kuenrg153/BitshokaNini_V1.1/3d/SOT-23-5_M5_MCH.step

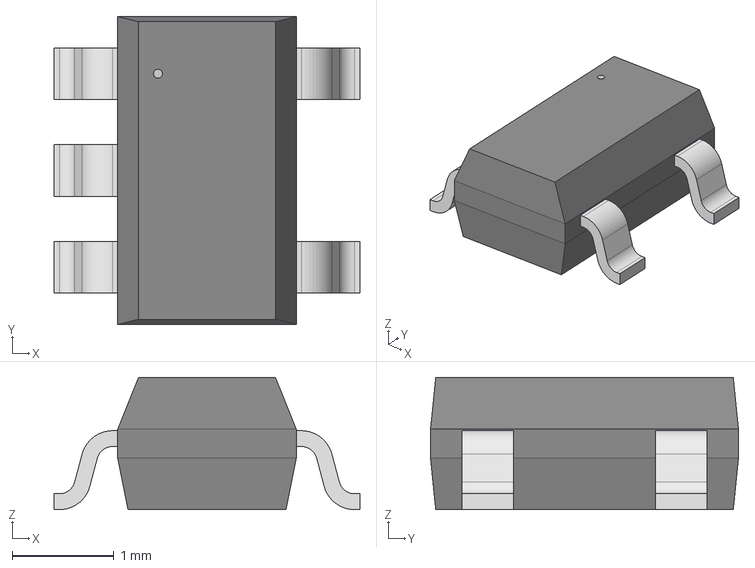
[picture p18: CAD file, 2025-06-05]
3d/SOT-23-5_M5_MCH.step
3.00 x 3.02 x 1.30 mm
