kuenrg153/BitshokaNini_V1.1/3d/DQH0008A.stp

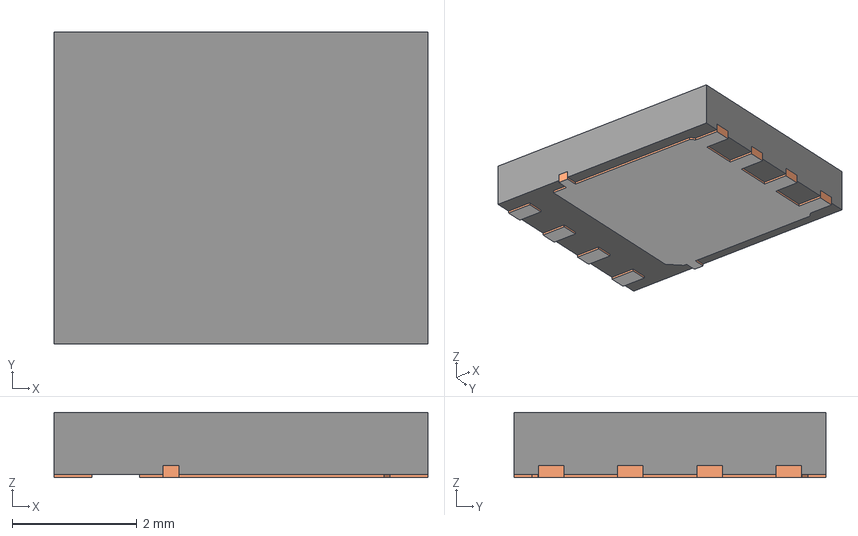
[picture p19: CAD file, 2025-06-05]
3d/DQH0008A.stp
6.00 x 5.00 x 1.05 mm
BODY-SON
FRAME-DQH0008A
PIN1-ID
