kuenrg153/BitshokaNini_V1.1/3d/Bitaxe_Heatsink.step

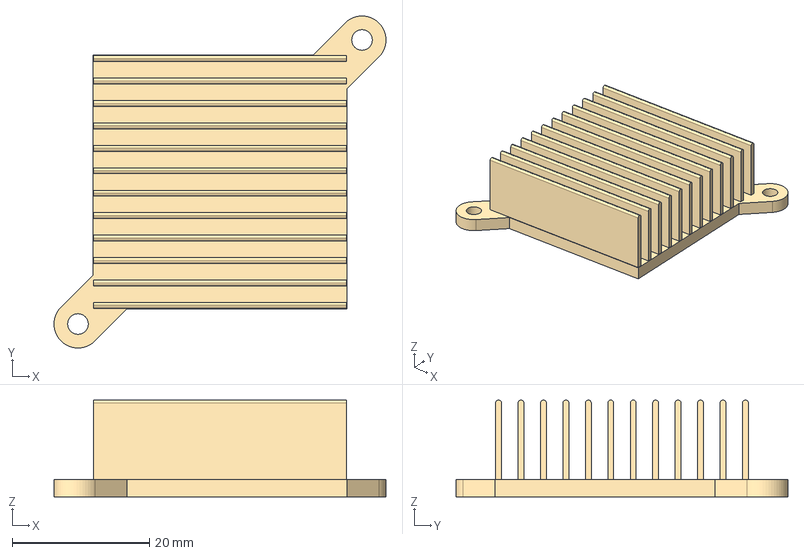
[picture p20: CAD file, 2025-06-05]
3d/Bitaxe_Heatsink.step
48.4 x 48.4 x 14.1 mm
