kuenrg153/BitshokaNini_V1.1/3d/oscillator3.2x2.5.step

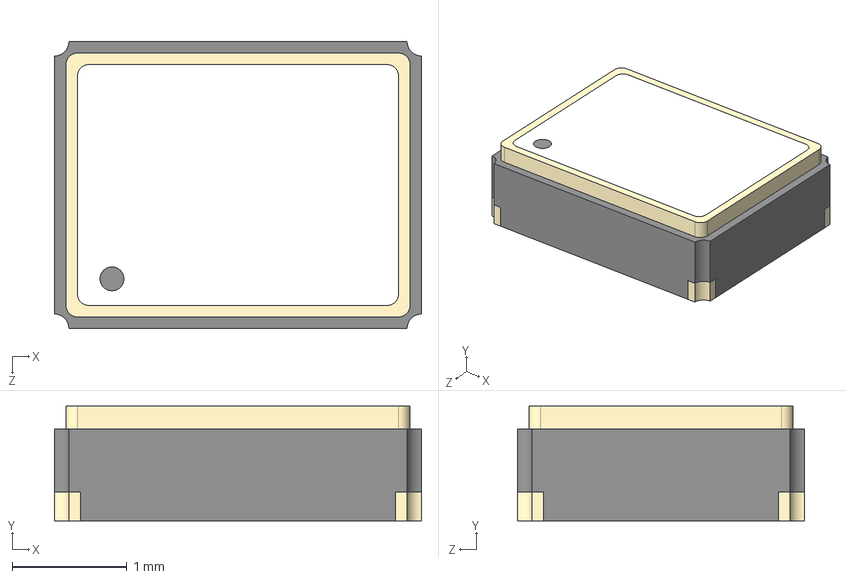
[picture p21: CAD file, 2025-06-05]
3d/oscillator3.2x2.5.step
3.20 x 1.00 x 2.50 mm
