kuenrg153/BitshokaNini_V1.1/3d/c-63862-1-r-3d.stp

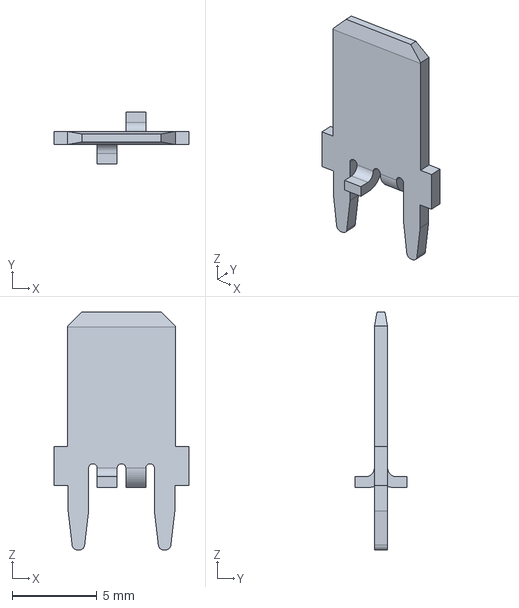
[picture p22: CAD file, 2025-06-05]
3d/c-63862-1-r-3d.stp
7.92 x 3.07 x 14.0 mm
