kuenrg153/BitshokaNini_V1.1/3d/2R5TPE220MAFB.step

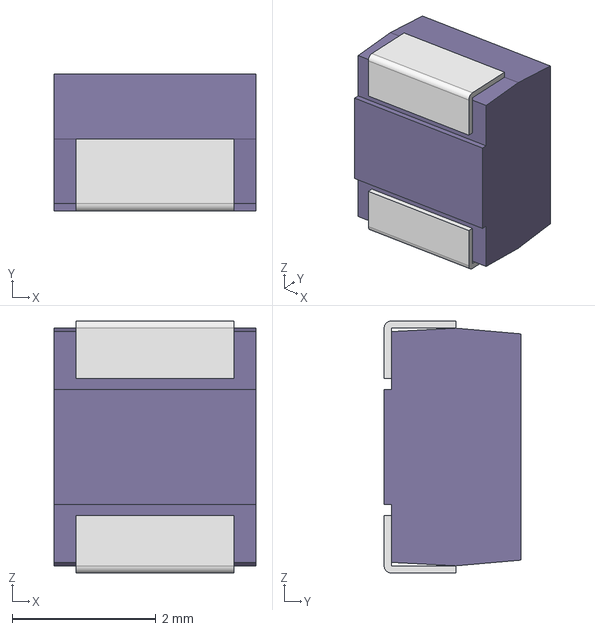
[picture p23: CAD file, 2025-06-05]
3d/2R5TPE220MAFB.step
2.80 x 1.90 x 3.50 mm
mold-B2
flame-B2 x 2
