kuenrg153/BitshokaNini_V1.1/3d/CS1213AG-tr.stp

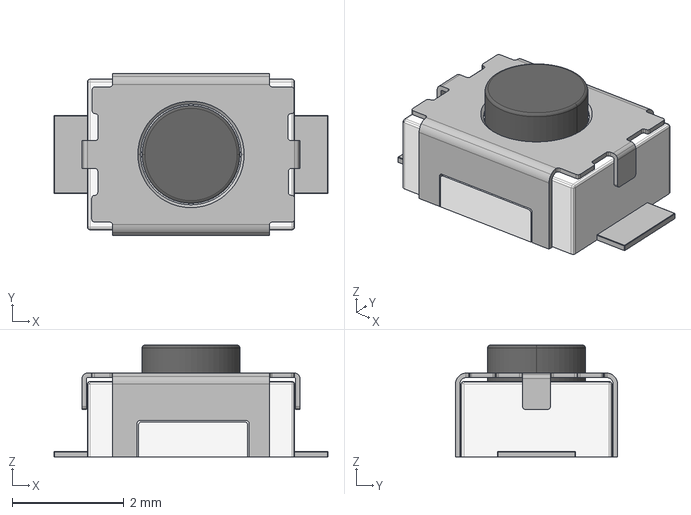
[picture p24: CAD file, 2025-06-05]
3d/CS1213AG-tr.stp
4.90 x 2.90 x 2.00 mm
