kuenrg153/BitshokaNini_V1.1/3d/CX3225SB16000H0FLJCC.STEP

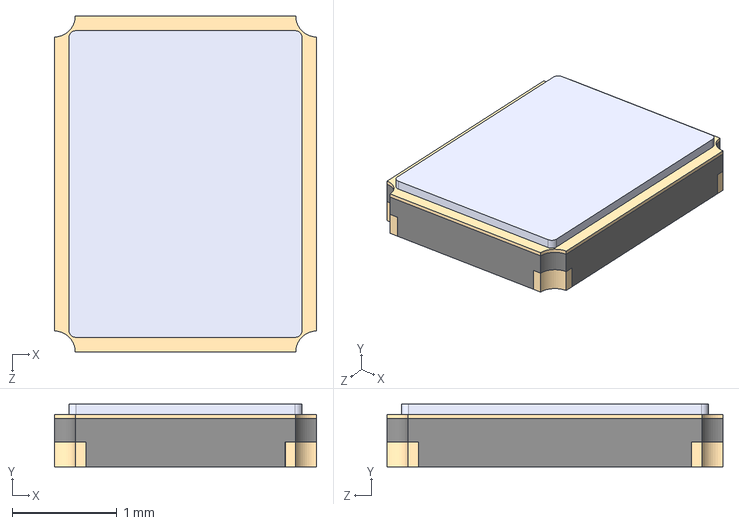
[picture p26: CAD file, 2025-06-05]
3d/CX3225SB16000H0FLJCC.STEP
2.50 x 0.6 x 3.20 mm
