kuenrg153/BitshokaNini_V1.1/3d/SN74AXC1T45DBVR.STEP

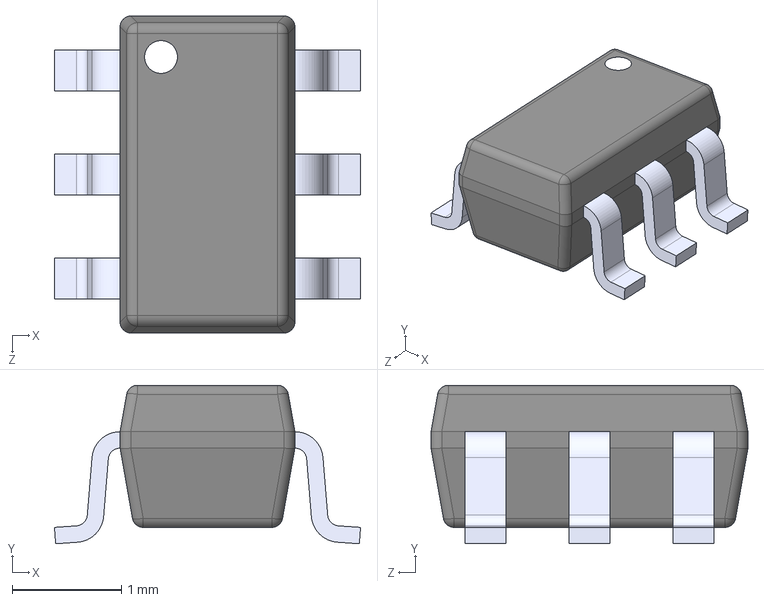
[picture p27: CAD file, 2025-06-05]
3d/SN74AXC1T45DBVR.STEP
2.80 x 1.45 x 2.90 mm
