kuenrg153/BitshokaNini_V1.1/3d/21-0164B_L622-1_MXM.step

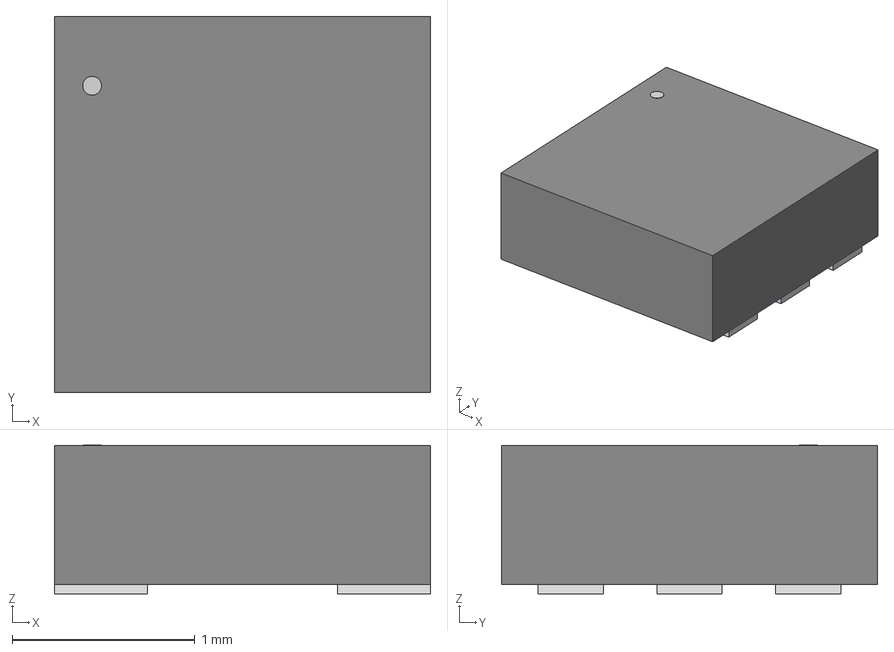
[picture p30: CAD file, 2025-06-05]
3d/21-0164B_L622-1_MXM.step
2.06 x 2.06 x 0.815 mm
