kuenrg153/BitshokaNini_V1.1/3d/54-00164.STEP

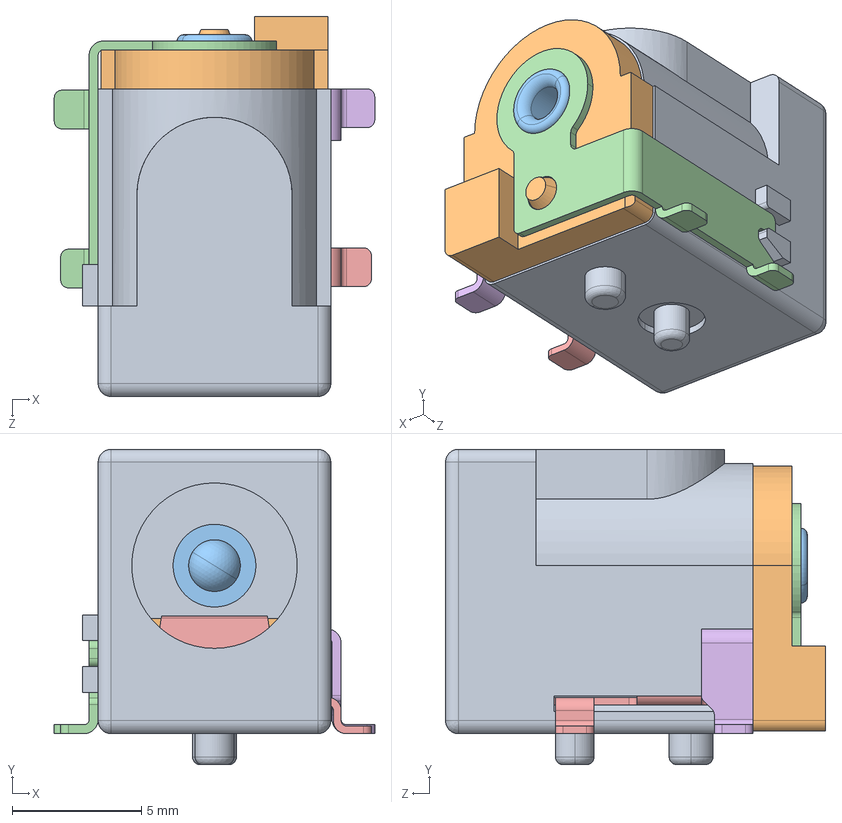
[picture p31: CAD file, 2025-06-05]
3d/54-00164.STEP
12.4 x 12.2 x 14.7 mm
54-00164_shell
54-00164_insulator
54-00164_center
54-00164_center contact
54-00164_spring contact
54-00164_shell contact
