kuenrg153/BitshokaNini_V1.1/3d/CUI_DEVICES_PJ-002AH.step

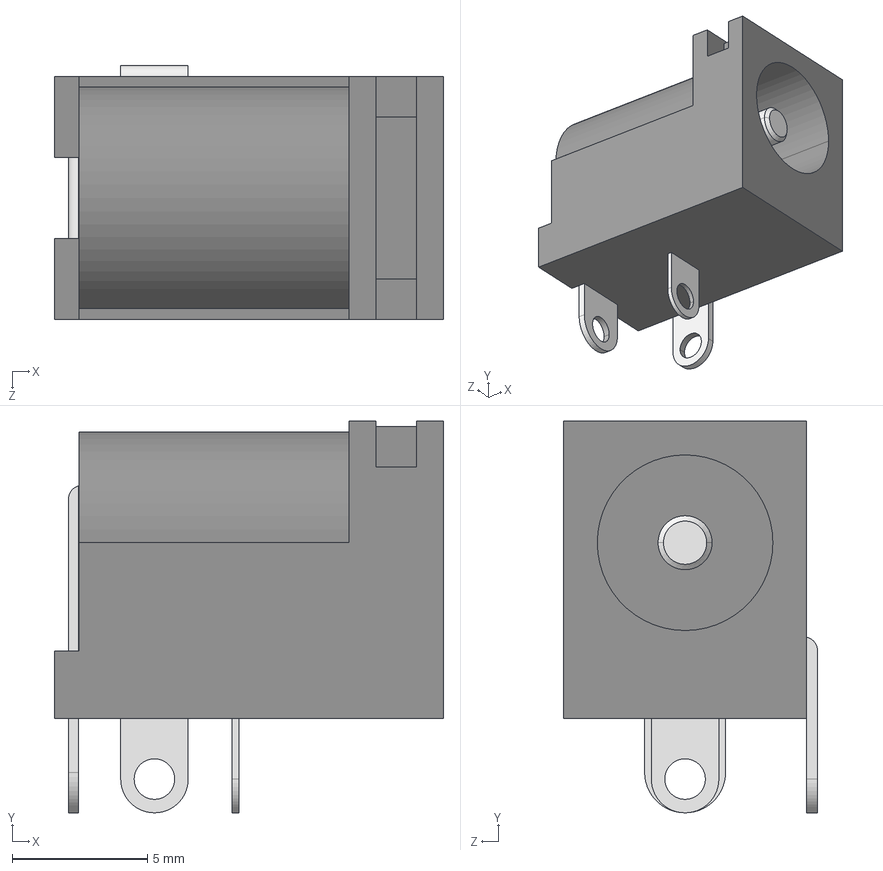
[picture p32: CAD file, 2025-06-05]
3d/CUI_DEVICES_PJ-002AH.step
14.4 x 14.5 x 9.40 mm
