kuenrg153/BitshokaNini_V1.1/3d/CUI_DEVICES_PJ-037AH.step

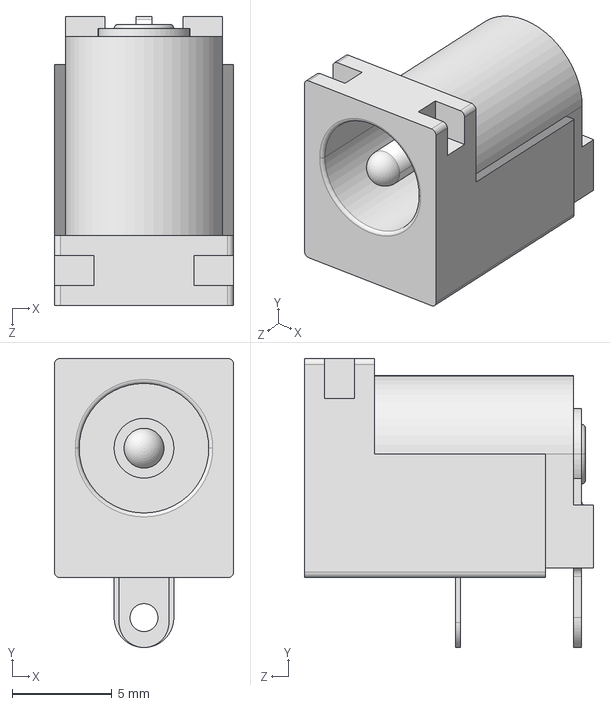
[picture p33: CAD file, 2025-06-05]
3d/CUI_DEVICES_PJ-037AH.step
9.00 x 14.5 x 14.5 mm
