kuenrg153/BitshokaNini_V1.1/3d/DQG0008A.stp

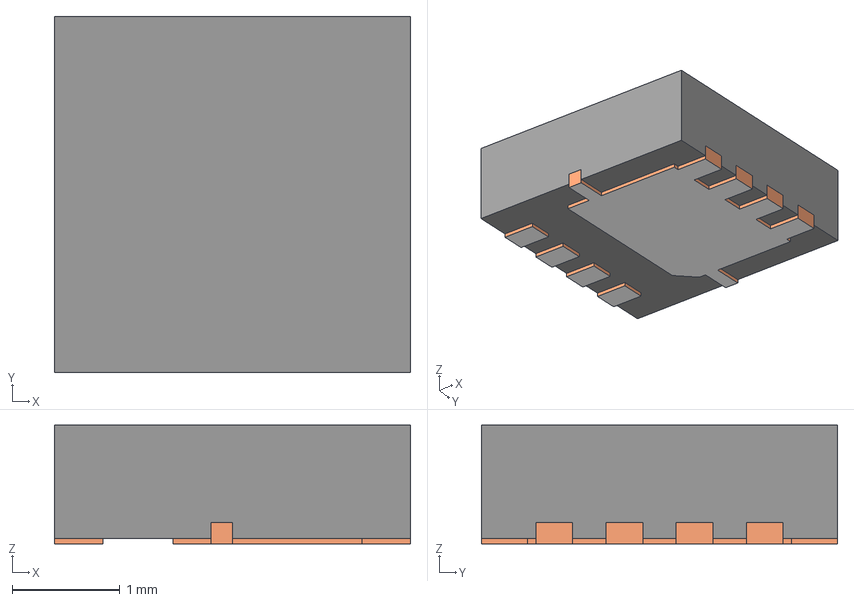
[picture p34: CAD file, 2025-06-05]
3d/DQG0008A.stp
3.30 x 3.30 x 1.10 mm
BODY-SON
FRAME-DQG0008A
PIN1-ID
