kuenrg153/BitshokaNini_V1.1/3d/SMV_z90.stp

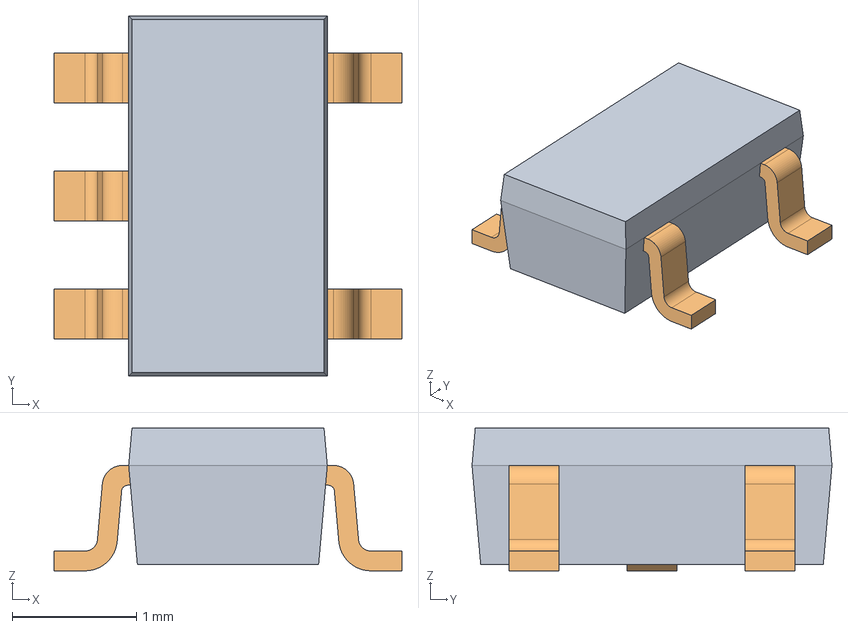
[picture p35: CAD file, 2025-06-05]
3d/SMV_z90.stp
2.80 x 2.90 x 1.15 mm
