kuenrg153/BitshokaNini_V1.1/3d/XRCGB27M120F3M10R0_MUR.step

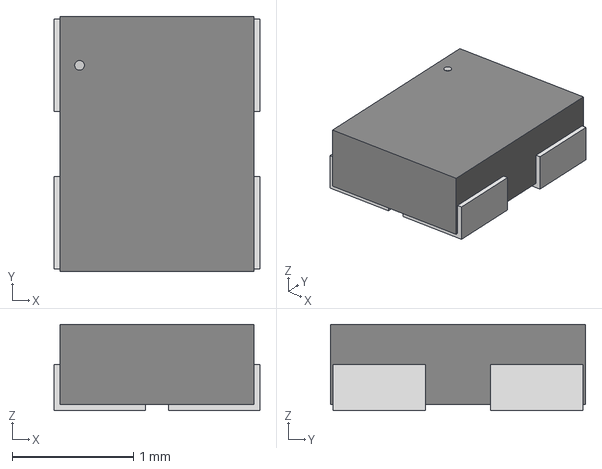
[picture p36: CAD file, 2025-06-05]
3d/XRCGB27M120F3M10R0_MUR.step
1.70 x 2.11 x 0.714 mm
