kuenrg153/BitshokaNini_V1.1/3d/FTSH-105-01-F-DV-K.stp

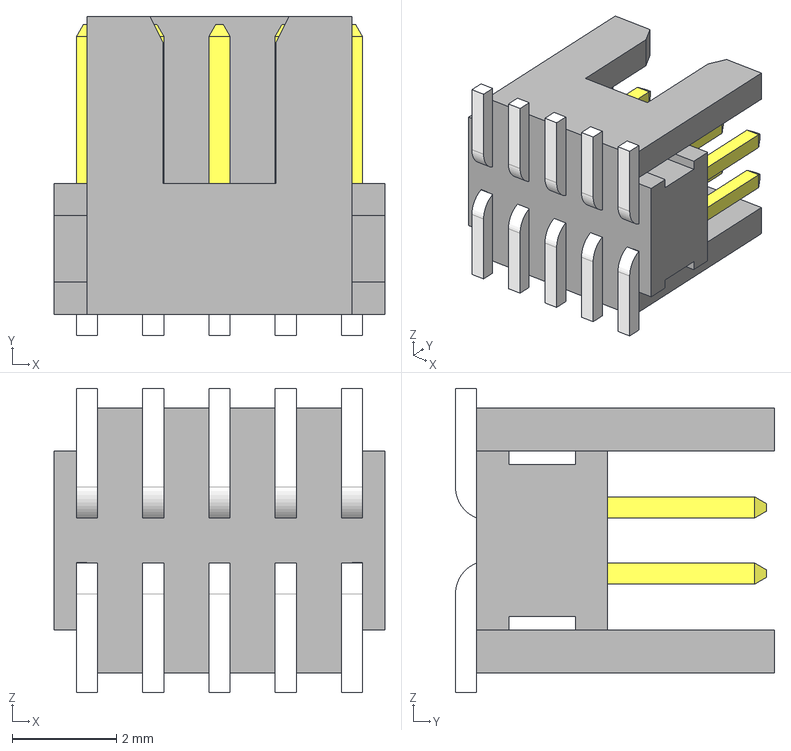
[picture p37: CAD file, 2025-06-05]
3d/FTSH-105-01-F-DV-K.stp
6.35 x 6.12 x 5.84 mm
FTSH-105-01-F-DV-K_pins2
FTSH-105-01-F-DV-K_pins1
FTSH-105-01-F-DV-K_body
