kuenrg153/BitshokaNini_V1.1/3d/DRL0006A.stp

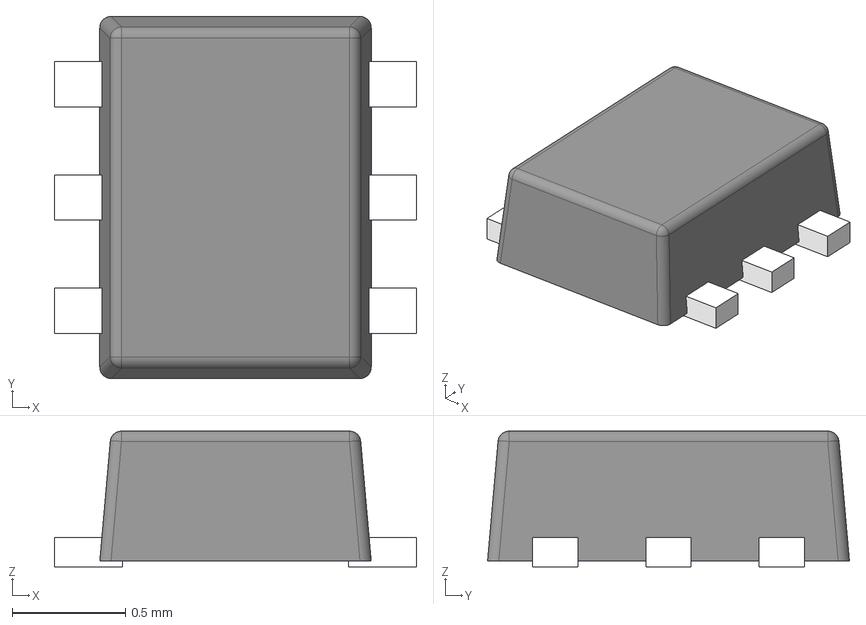
[picture p38: CAD file, 2025-06-05]
3d/DRL0006A.stp
1.60 x 1.60 x 0.6 mm
FRAME-DRL0006A
BODY-SOT
PIN1-ID
