kuenrg153/BitshokaNini_V1.1/3d/PLCC6_LED_3_5X3_4X2_8_CRW.step

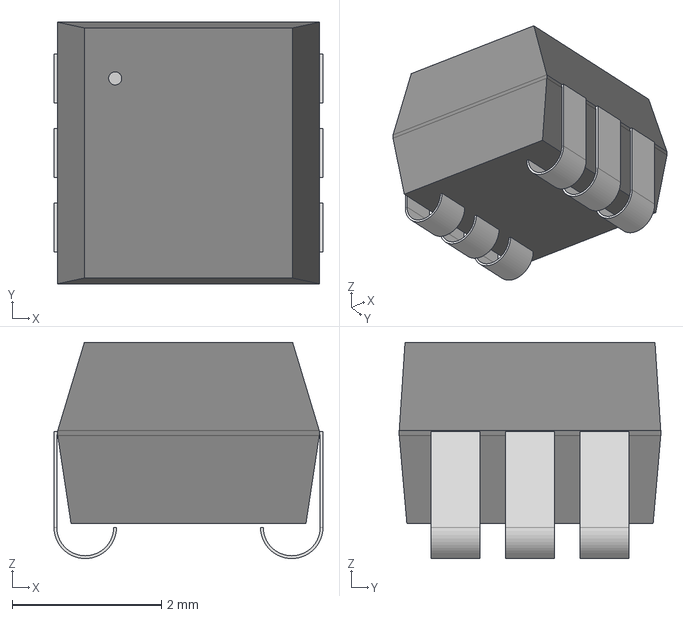
[picture p39: CAD file, 2025-06-05]
3d/PLCC6_LED_3_5X3_4X2_8_CRW.step
3.61 x 3.51 x 2.90 mm
