kuenrg153/BitshokaNini_V1.1/3d/SW_CS1213AGF260_CRS.step

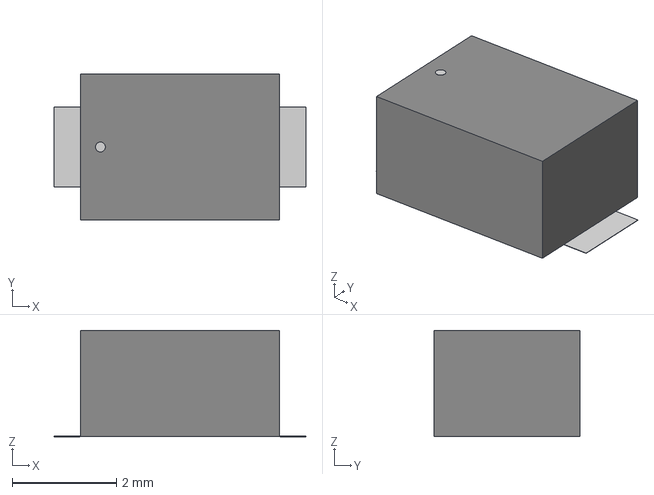
[picture p40: CAD file, 2025-06-05]
3d/SW_CS1213AGF260_CRS.step
4.83 x 2.79 x 2.04 mm
