kuenrg153/BitshokaNini_V1.1/3d/Coilcraft-SLC1175.STEP

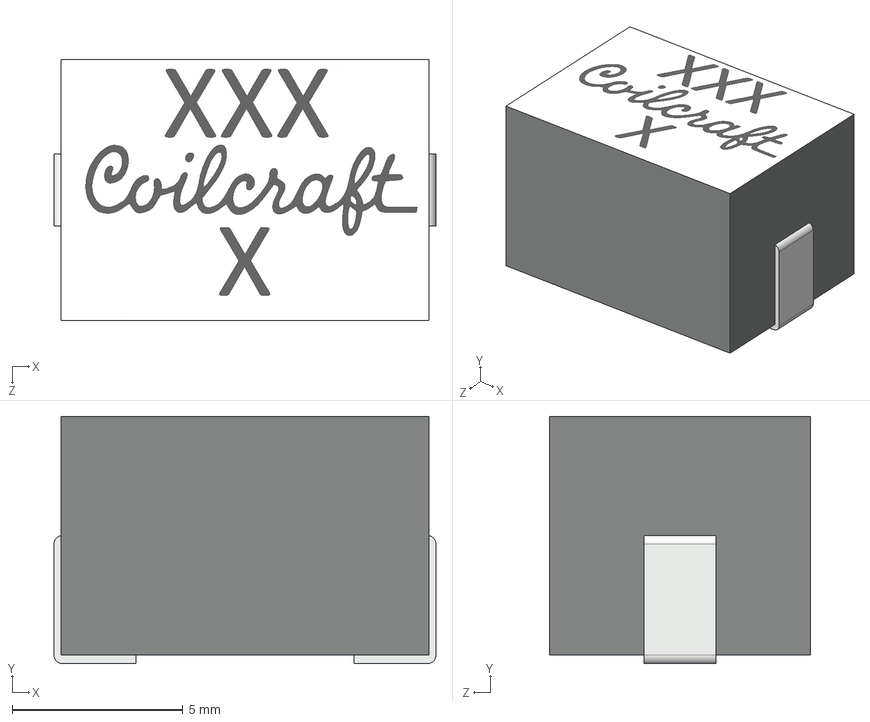
[picture p41: CAD file, 2025-06-05]
3d/Coilcraft-SLC1175.STEP
11.2 x 7.25 x 7.65 mm
